DosFox1/FoxSCSI---An-Apple-ii-SCSI-Card-/Renders/Apple ii SCSI Hi Res Bottom Side.png

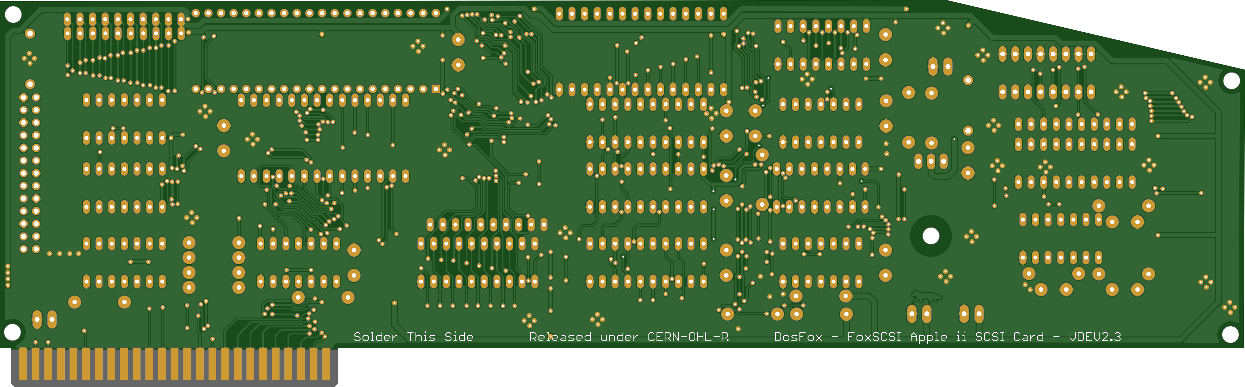
Renders/Apple ii SCSI Hi Res Bottom Side.png
